d123ij/vr5000_display/images/display_picture.png

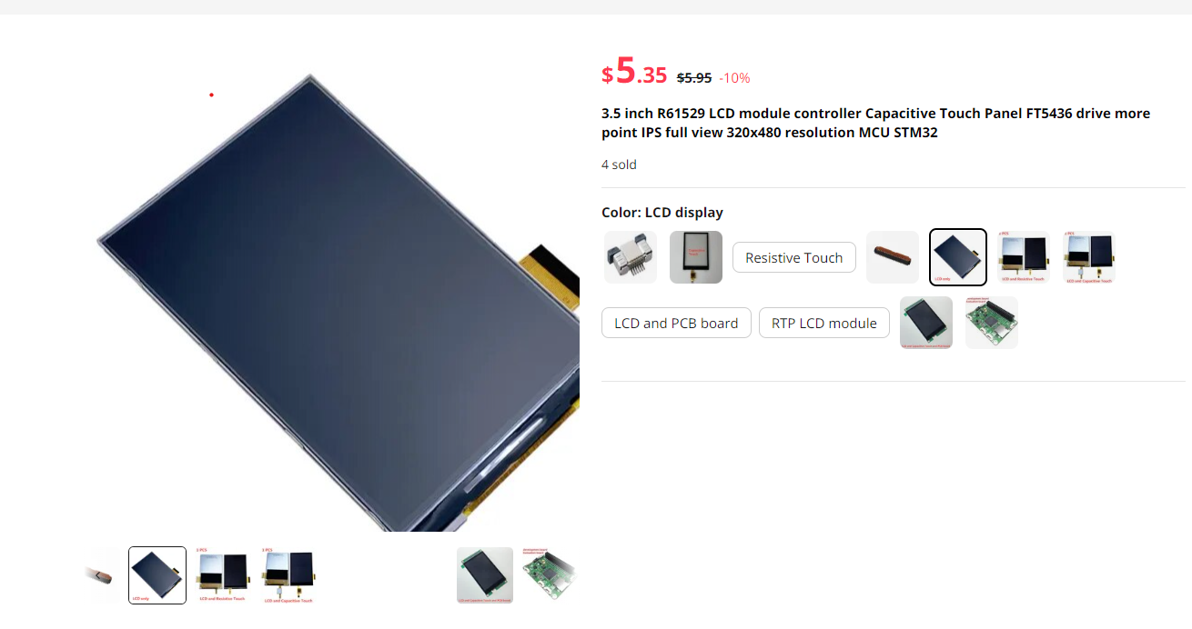
images/display_picture.png
