d123ij/vr5000_display/images/IMGP0145 [].JPG

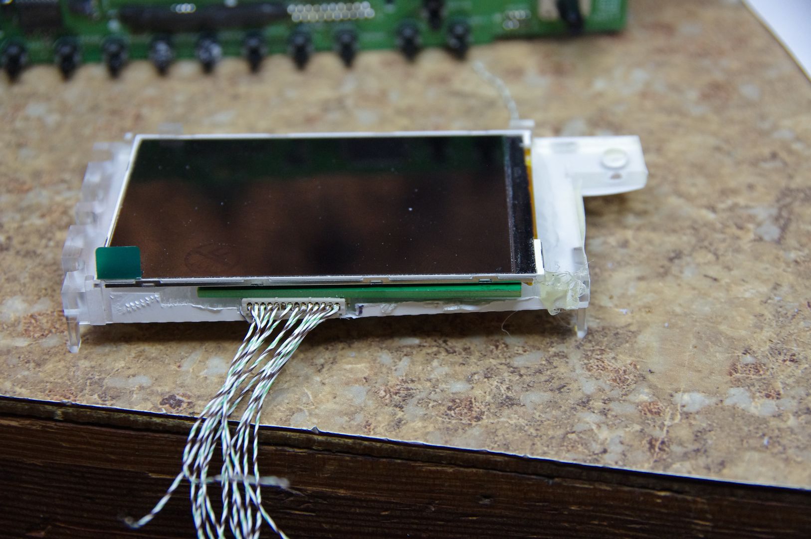
images/IMGP0145 [].JPG
