d123ij/vr5000_display/images/IMGP0148 [].JPG

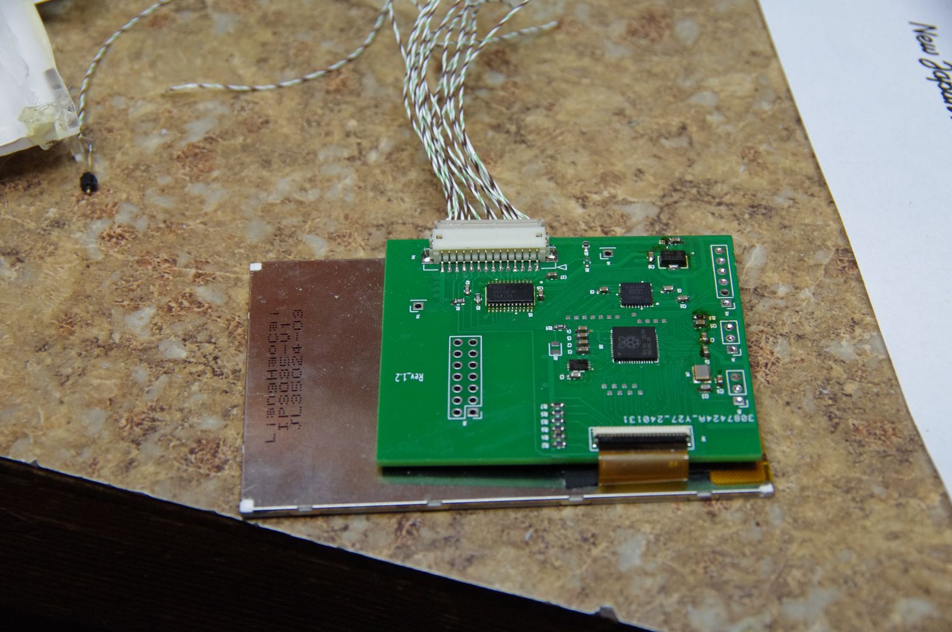
images/IMGP0148 [].JPG
