d123ij/vr5000_display/images/IMGP0149 [].JPG

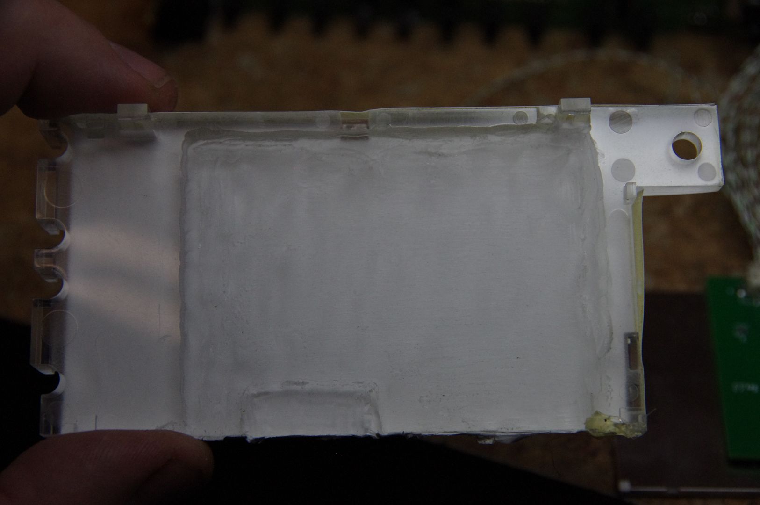
images/IMGP0149 [].JPG
