d123ij/vr5000_display/images/IMGP0150 [].JPG

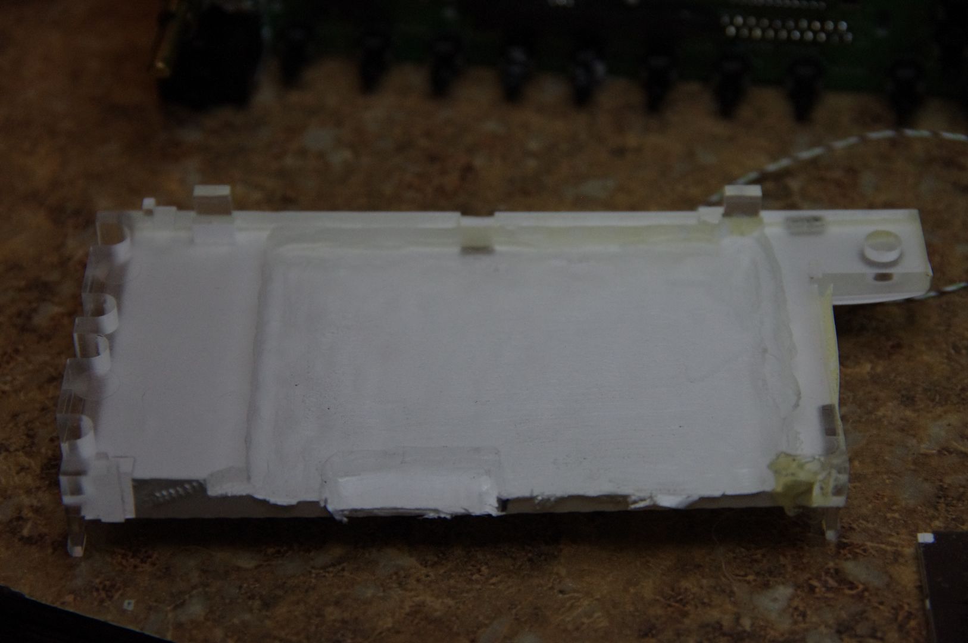
images/IMGP0150 [].JPG
