d123ij/vr5000_display/images/IMGP0155 [].JPG

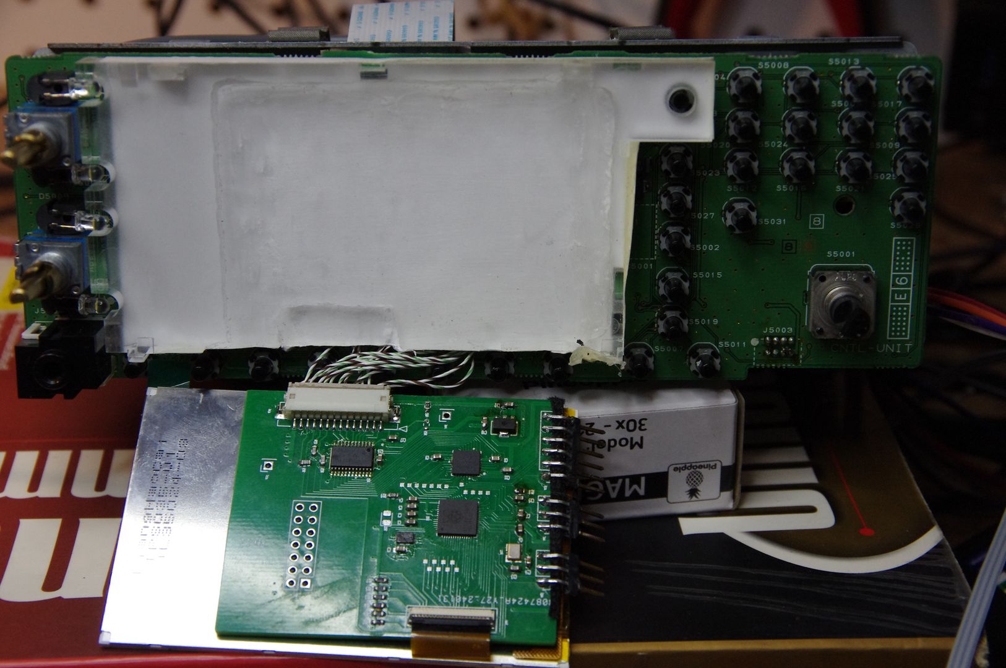
images/IMGP0155 [].JPG
