d123ij/vr5000_display/images/IMGP0156 [].JPG

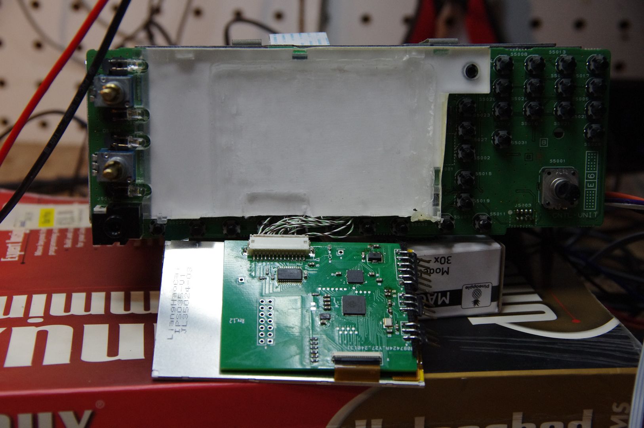
images/IMGP0156 [].JPG
