d123ij/vr5000_display/images/IMGP0157 [].JPG

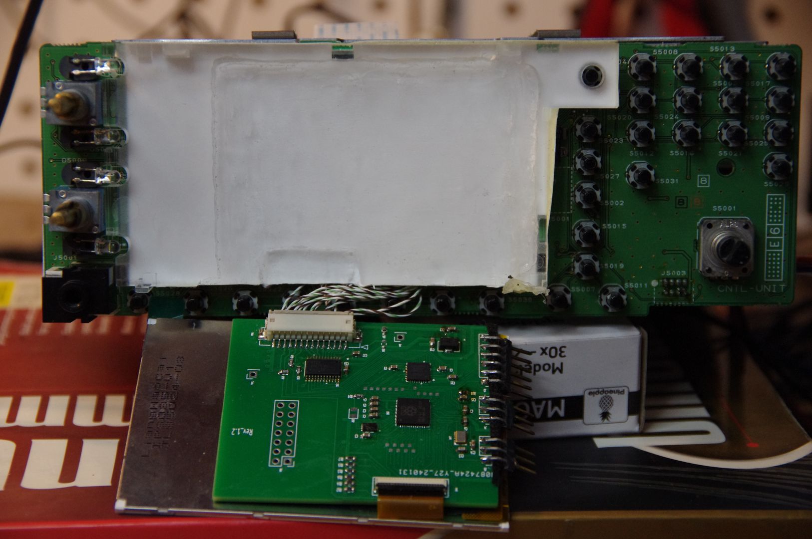
images/IMGP0157 [].JPG
