d123ij/vr5000_display/images/IMGP0162 [].JPG

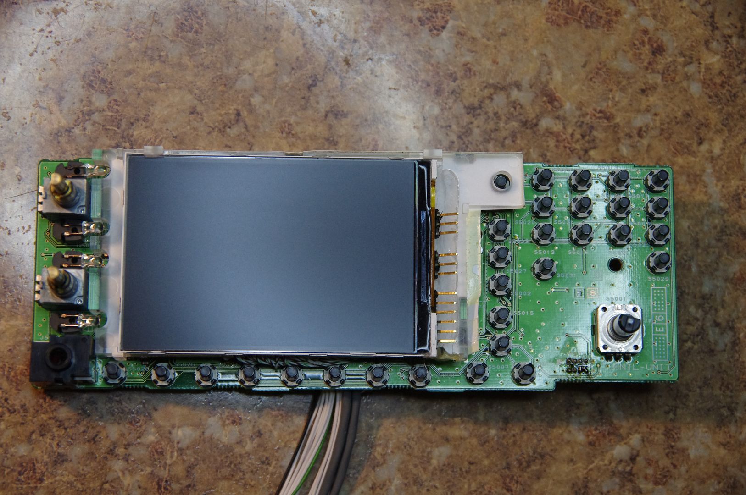
images/IMGP0162 [].JPG
