d123ij/vr5000_display/images/IMGP0163 [].JPG

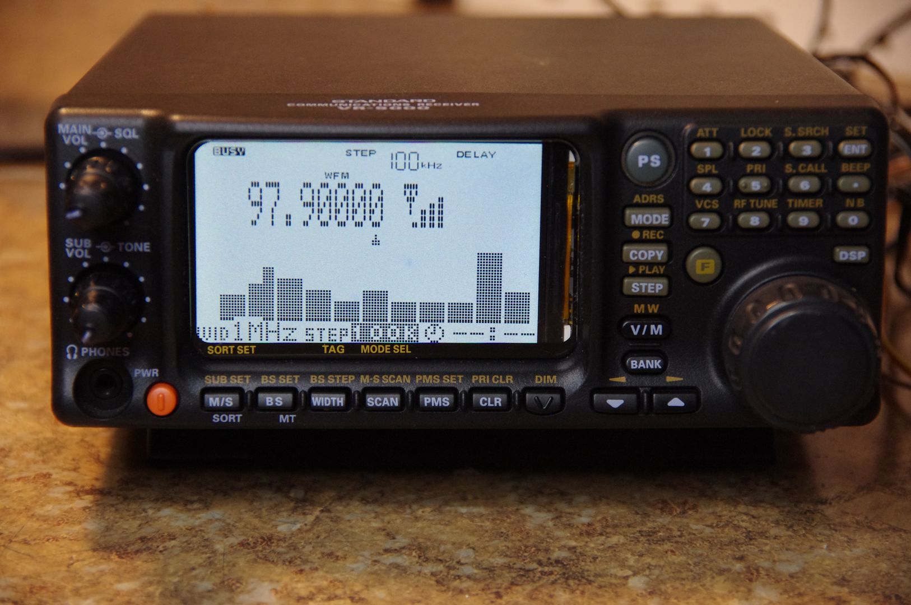
images/IMGP0163 [].JPG
