d123ij/vr5000_display/images/IMGP0164 [].JPG

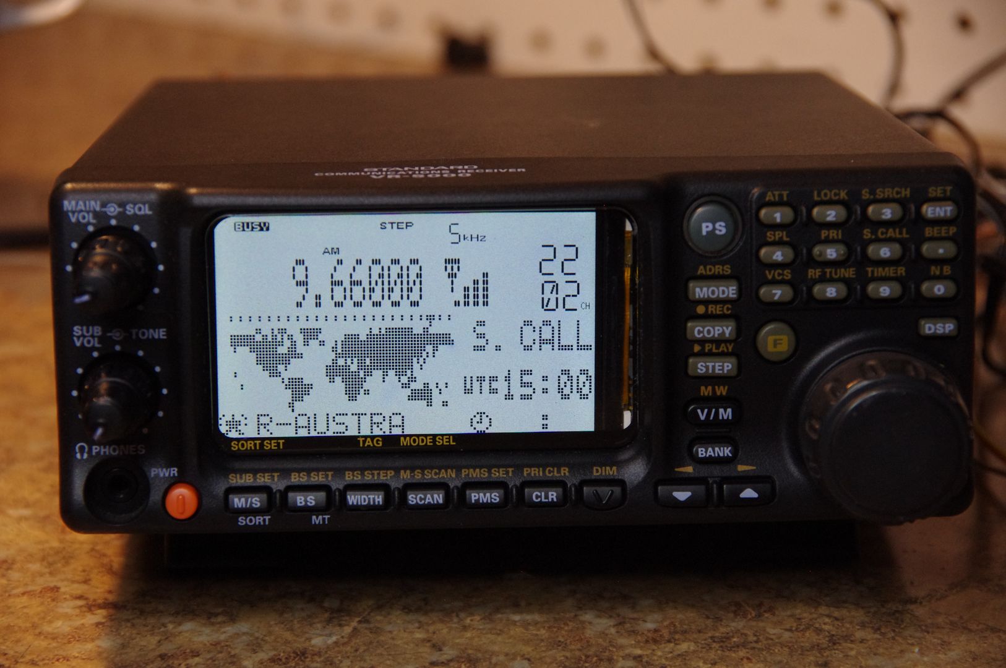
images/IMGP0164 [].JPG
