d123ij/vr5000_display/vr5000_rp2040/pico-freertos-sample/vr5000_disp/disp_font.h

#ifndef FONT_TABLE
#define FONT_TABLE
//font table
const uint8_t Font1611_Table[] =
{
// @0 'l' (11 pixels wide)
0x00, 0x00, //
0x7F, 0xE0, // ##########
0xCF, 0xE0, //##  #######
0xCF, 0xE0, //##  #######
0xCF, 0xE0, //##  #######
0xCF, 0xE0, //##  #######
0xCF, 0xE0, //##  #######
0xC0, 0x60, //##       ##
0xC0, 0x60, //##       ##
0x7F, 0xE0, // ##########
0x00, 0x00, //
0x00, 0x00, //
0x00, 0x00, //
0x00, 0x00, //
0x00, 0x00, //
0x00, 0x00, //

// @32 'o' (11 pixels wide)
0x00, 0x00, //
0x00, 0x00, //
0x80, 0x00, //
0x80, 0x00, //
0xFF, 0xE0, //############
0xFF, 0xE0, //############
0xFF, 0xE0, //############
0x8E, 0x00, //     ###
0x8E, 0x00, //     ###
0x0E, 0x00, //     ###
0x00, 0x00, //
0x00, 0x00, //
0x00, 0x00, //
0x00, 0x00, //
0x00, 0x00, //
0x00, 0x00, //

// @64 'c' (11 pixels wide)
0x00, 0x00, //
0x00, 0x00, //
0x00, 0x00, //
0x00, 0x00, //
0xFF, 0x80, //############
0xFF, 0x80, //############
0xFF, 0x80, //############
0x1C, 0x00, //     ###
0x1C, 0x00, //     ###
0x1C, 0x00, //     ###
0x00, 0x00, //
0x00, 0x00, //
0x00, 0x00, //
0x00, 0x00, //
0x00, 0x00, //
0x00, 0x00, //

// @96 'f' (11 pixels wide)
0x00, 0x00, //
0x7F, 0xC0, // ##########
0xC0, 0x60, //##        ##
0xC0, 0x60, //##        ##
0xCF, 0xE0, //##  ########
0xCF, 0xE0, //##  ########
0xC0, 0xE0, //##       ###
0xC0, 0xE0, //##       ###
0xCF, 0xE0, //##  ########
0xCF, 0xE0, //##  ########
0xCF, 0xE0, //##  ########
0x7F, 0xC0, // ##########
0x00, 0x00, //
0x00, 0x00, //
0x00, 0x00, //
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
0xFF, 0xFF, //###########
0xFF, 0xFF, //###########
0xFF, 0xFF, //###########
0xFF, 0xFF, //###########
0xFF, 0xFF, //###########
0xFF, 0xFF, //###########
0xFF, 0xFF, //###########
0xFF, 0xFF, //###########
0xFF, 0xFF, //###########
0xFF, 0xFF, //###########

};

#endif 
